iotdevspot/atmega328-driven-ws2811-led-strip-driver-with-at-09-bluetooth/images/5.png

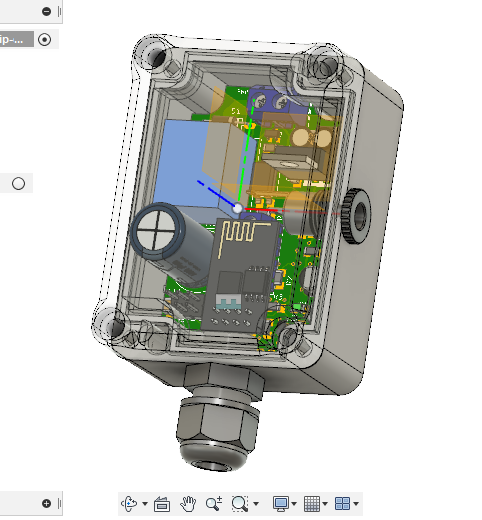
images/5.png
